crnicholson/MothCam/Code/backend/examples/mothOne.png

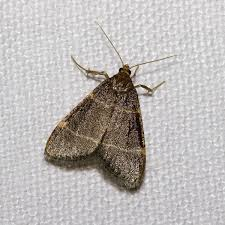
Code/backend/examples/mothOne.png
