crnicholson/MothCam/Code/backend/examples/mothSeven.png

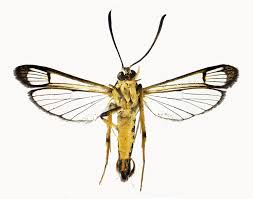
Code/backend/examples/mothSeven.png
