crnicholson/MothCam/PCBs + Schematic/mothCam/mothCam.kicad_sch

## KiCad design PCBs + Schematic/mothCam/mothCam.kicad_sch (2024-12-31)

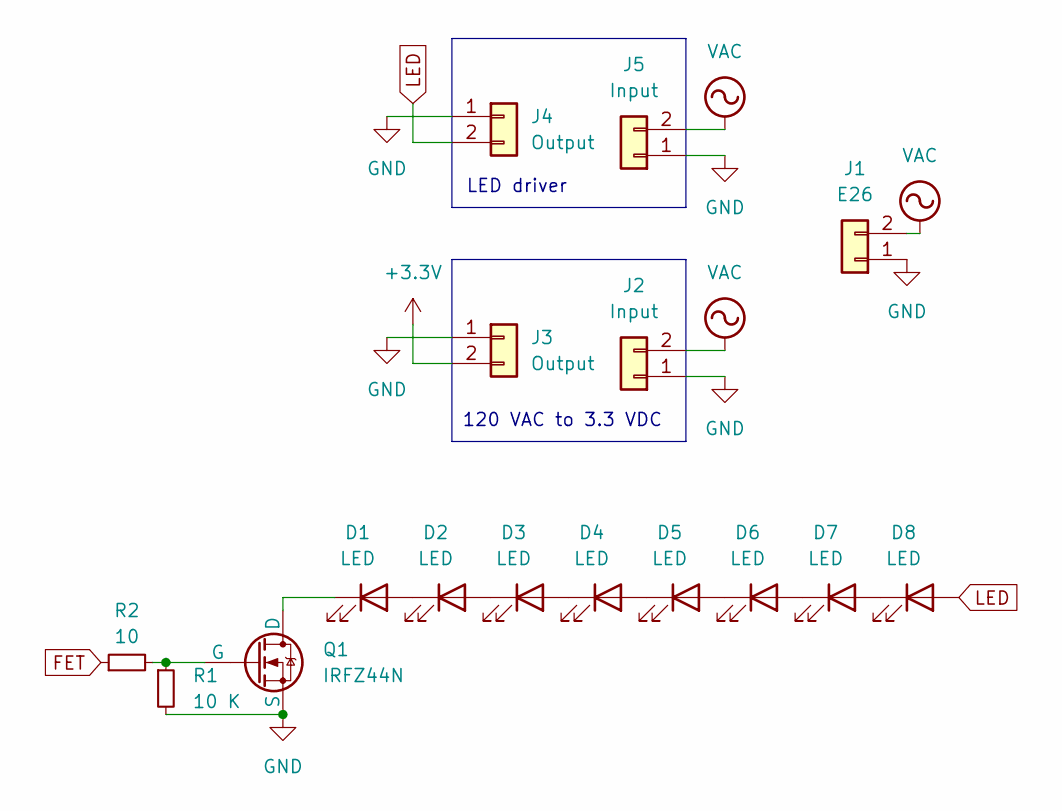
[picture p10: schematic mothCam.kicad_sch]

Parts:
D1, D2, D3, D4, D5, D6, D7, D8: LED
J1: E26
J2, J5: Input
J3, J4: Output
Q1: IRFZ44N
R1: 10 K
R2: 10

Connections:
+3.3V: J3.2
FET: R2.1
GND: J1.1, J2.1, J3.1, J4.1, J5.1, Q1.3 (S), R1.2
LED: D8.2 (A), J4.2
unnamed: D1.1 (K), Q1.1 (D)
unnamed: D1.2 (A), D2.1 (K)
unnamed: D2.2 (A), D3.1 (K)
unnamed: D3.2 (A), D4.1 (K)
unnamed: D4.2 (A), D5.1 (K)
unnamed: D5.2 (A), D6.1 (K)
unnamed: D6.2 (A), D7.1 (K)
unnamed: D7.2 (A), D8.1 (K)
unnamed: Q1.2 (G), R1.1, R2.2
VAC: J1.2, J2.2, J5.2

Notes on the sheet:
120 VAC to 3.3 VDC
LED driver
